vmodamio/typewrt_mark2/images/PXL_20260221_143158114.jpg

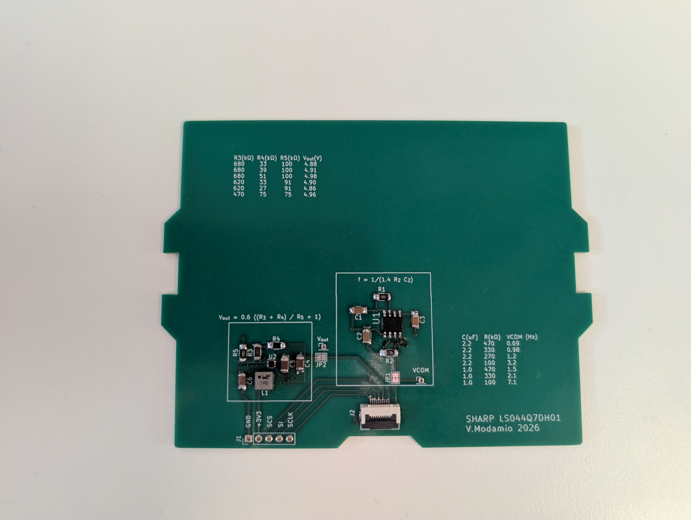
images/PXL_20260221_143158114.jpg
