vmodamio/typewrt_mark2/images/PXL_20260221_143226944.jpg

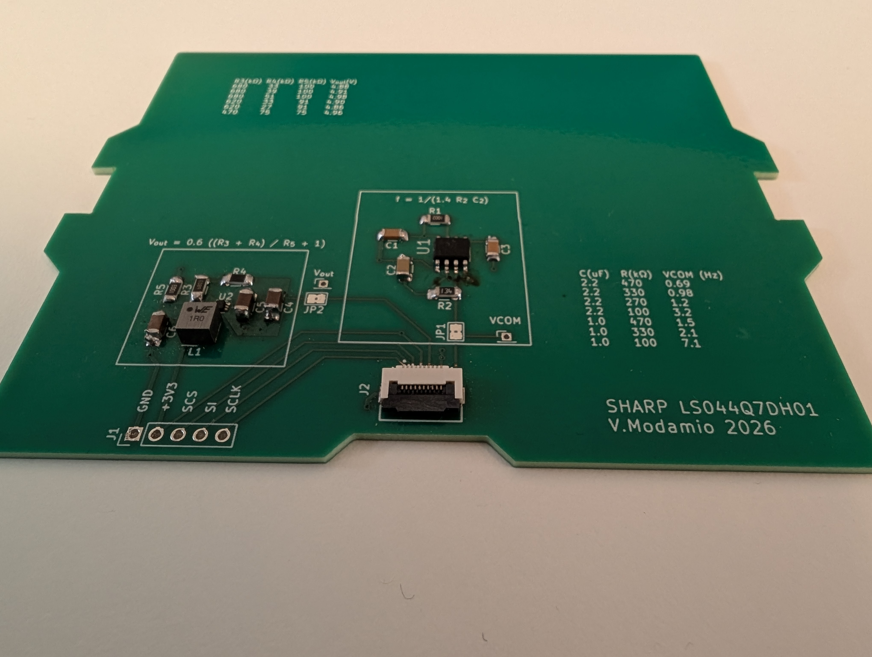
images/PXL_20260221_143226944.jpg
