vmodamio/typewrt_mark2/images/PXL_20260221_143322135.jpg

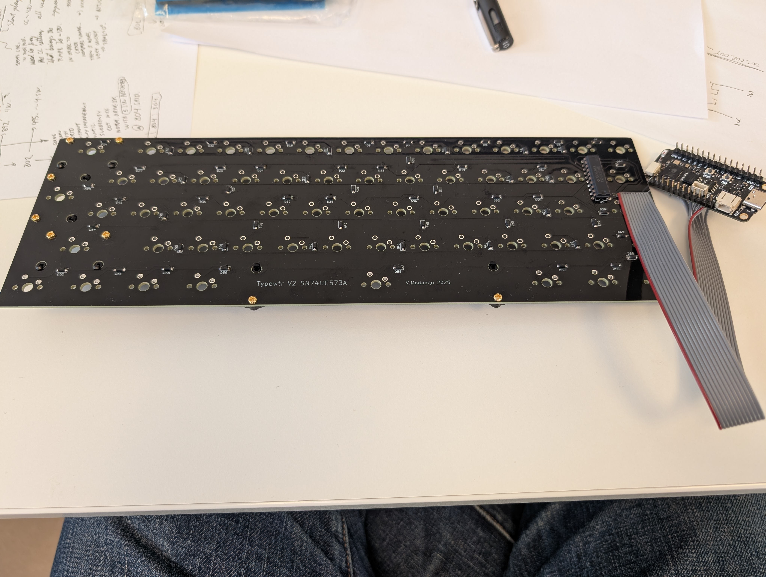
images/PXL_20260221_143322135.jpg
