vmodamio/typewrt_mark2/images/PXL_20260221_143605408.jpg

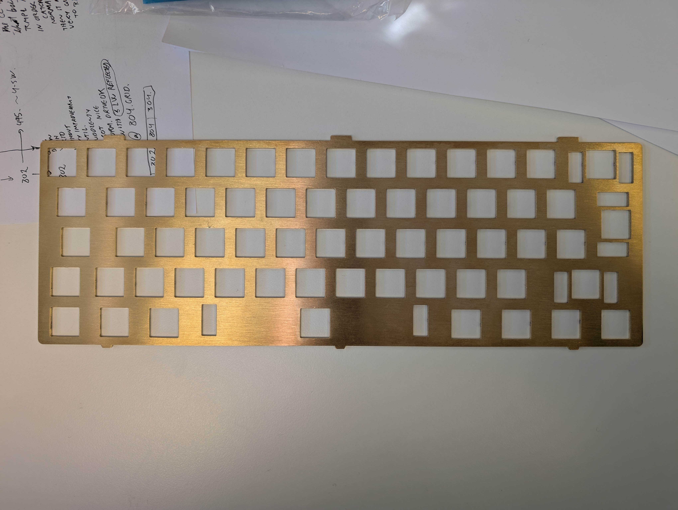
images/PXL_20260221_143605408.jpg
