vmodamio/typewrt_mark2/images/PXL_20260221_144143842.jpg

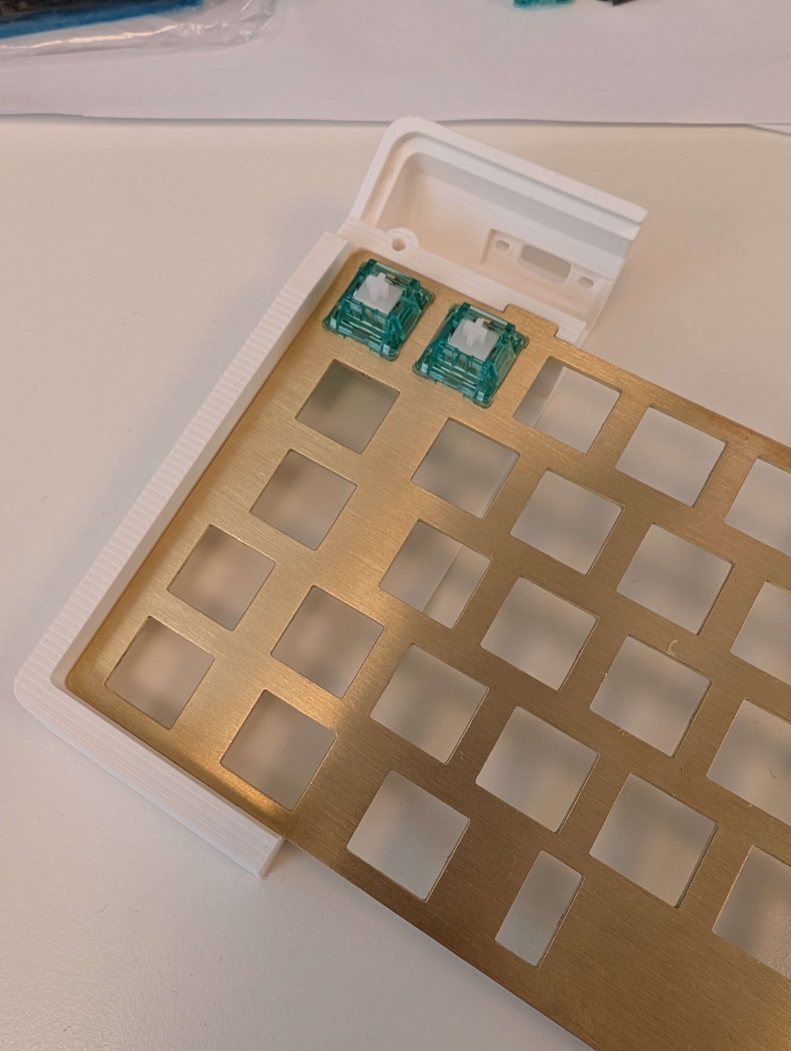
images/PXL_20260221_144143842.jpg
