vmodamio/typewrt_mark2/images/PXL_20260221_162343573.jpg

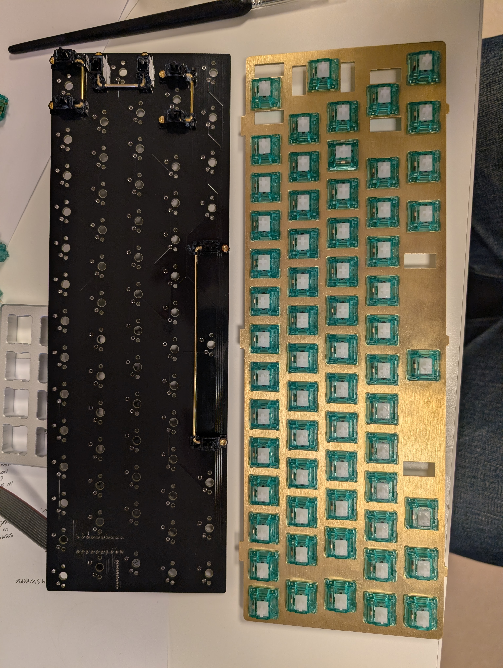
images/PXL_20260221_162343573.jpg
