vmodamio/typewrt_mark2/images/PXL_20260221_164626102.jpg

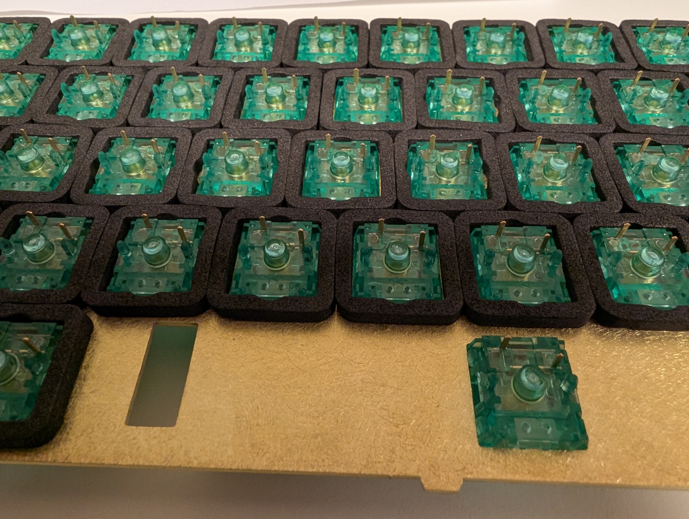
images/PXL_20260221_164626102.jpg
