vmodamio/typewrt_mark2/images/PXL_20260221_170008910.jpg

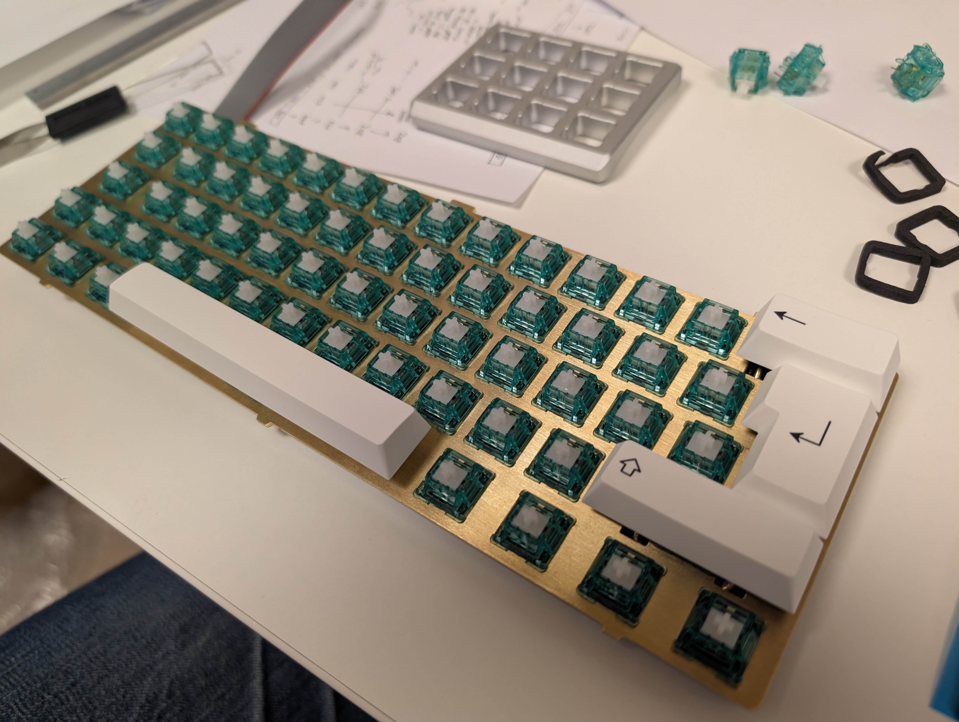
images/PXL_20260221_170008910.jpg
