vmodamio/typewrt_mark2/images/PXL_20260225_174053376.jpg

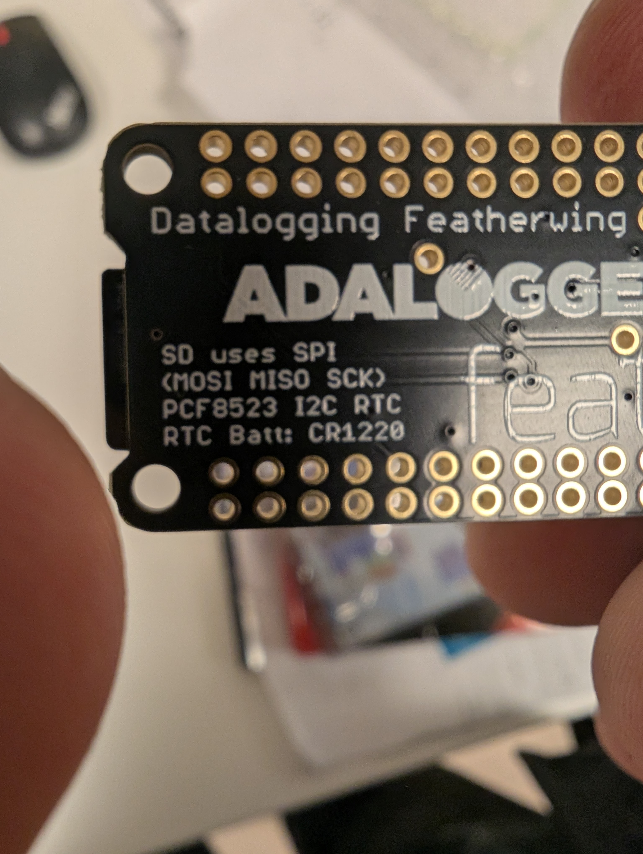
images/PXL_20260225_174053376.jpg
