vmodamio/typewrt_mark2/images/PXL_20260226_163334351.jpg

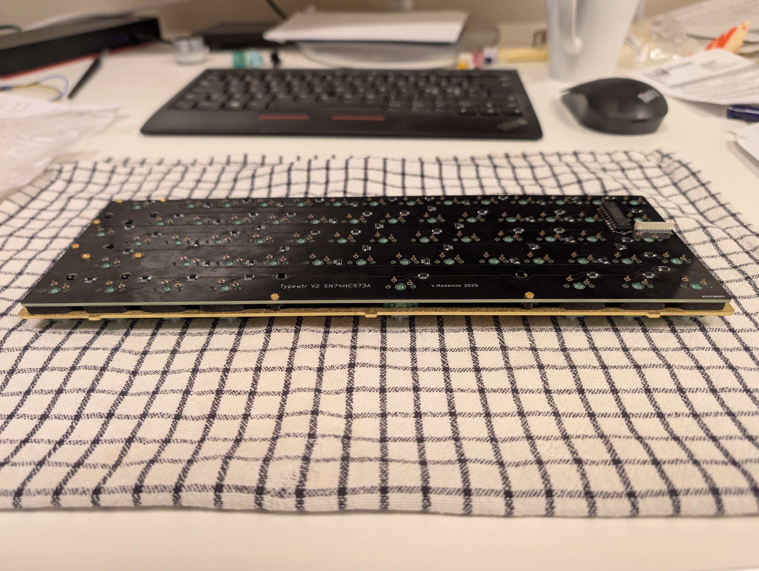
images/PXL_20260226_163334351.jpg
