vmodamio/typewrt_mark2/images/PXL_20260226_163400330.jpg

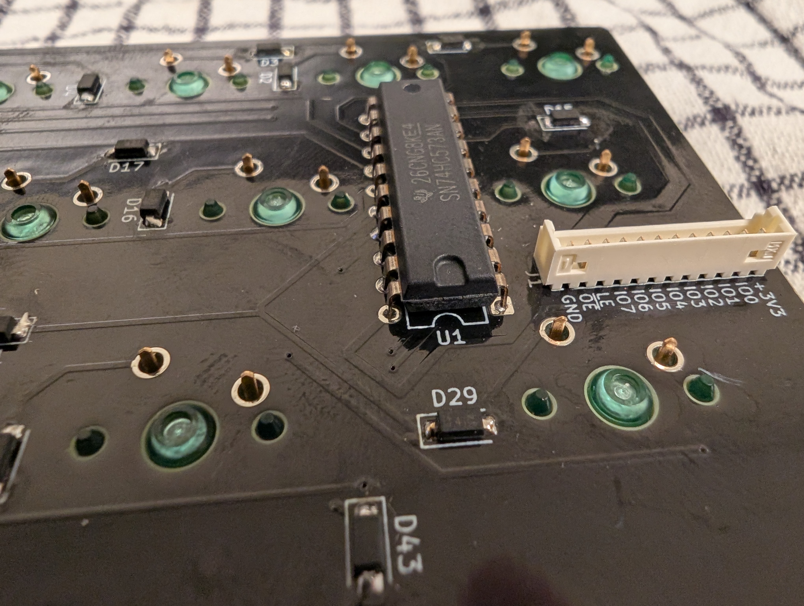
images/PXL_20260226_163400330.jpg
