vmodamio/typewrt_mark2/images/PXL_20260226_171633892.jpg

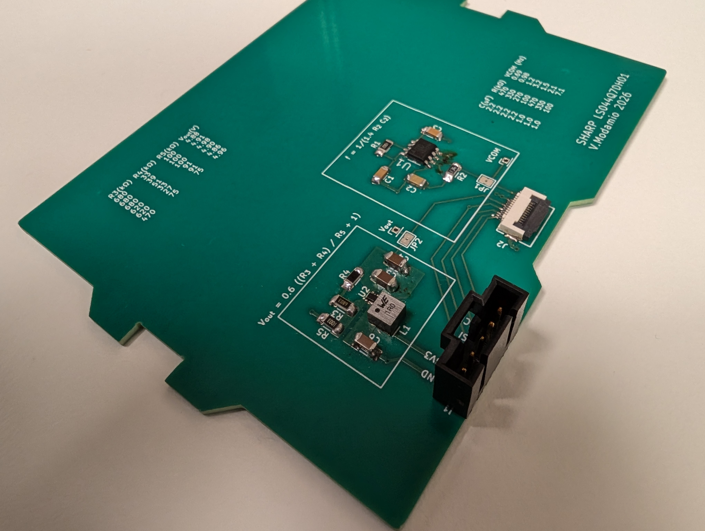
images/PXL_20260226_171633892.jpg
