vmodamio/typewrt_mark2/images/PXL_20260226_174025319.jpg

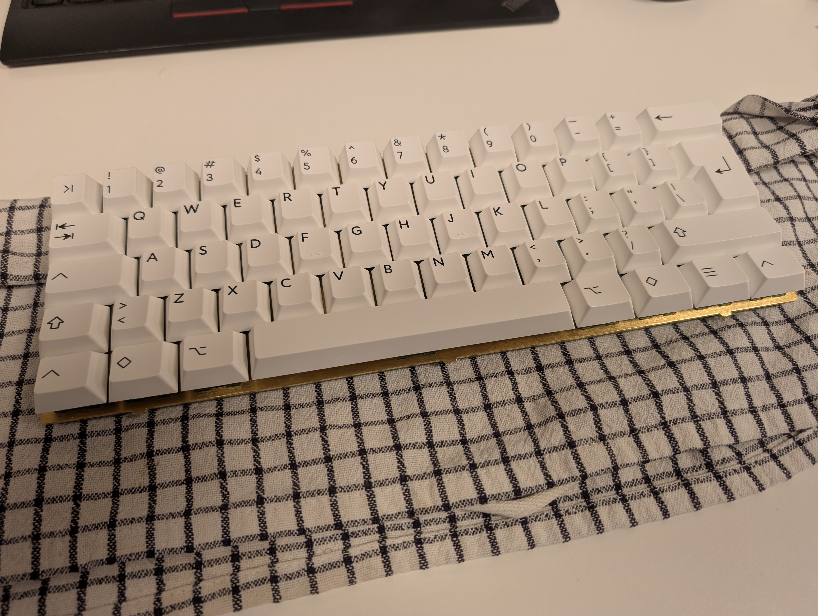
images/PXL_20260226_174025319.jpg
