vmodamio/typewrt_mark2/images/PXL_20260226_174041446.jpg

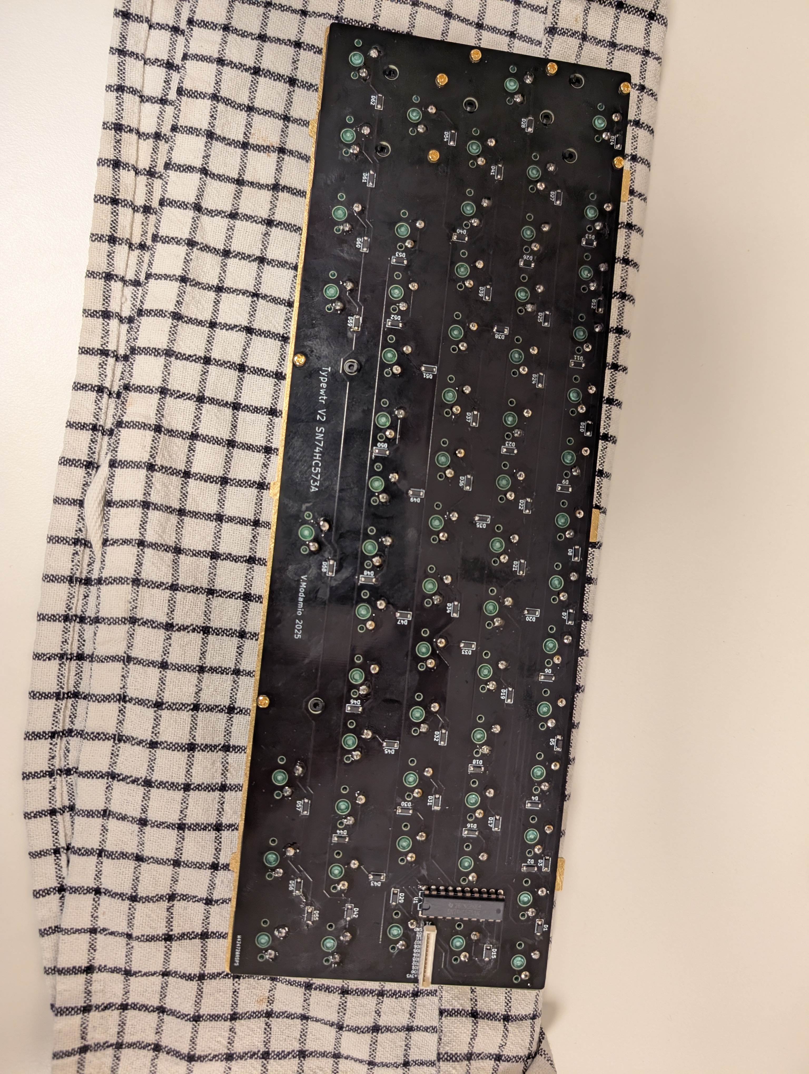
images/PXL_20260226_174041446.jpg
