vmodamio/typewrt_mark2/images/PXL_20260314_165601002.jpg

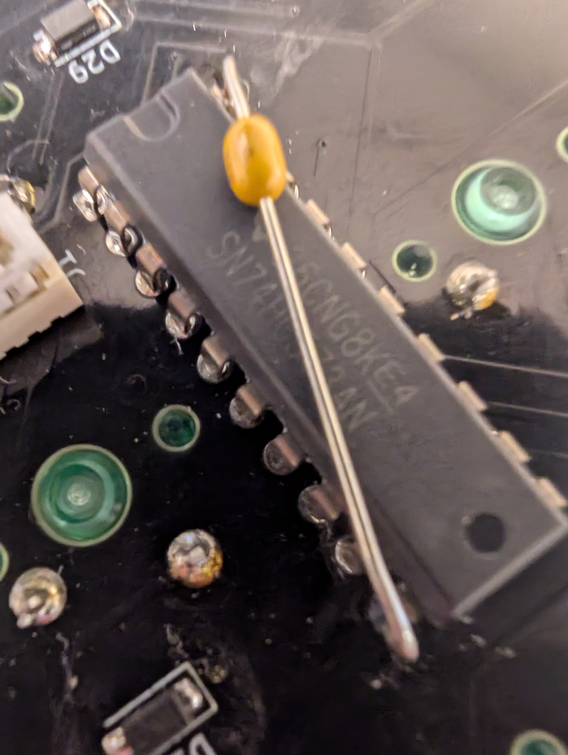
images/PXL_20260314_165601002.jpg
