vmodamio/typewrt_mark2/images/PXL_20260410_063325487.jpg

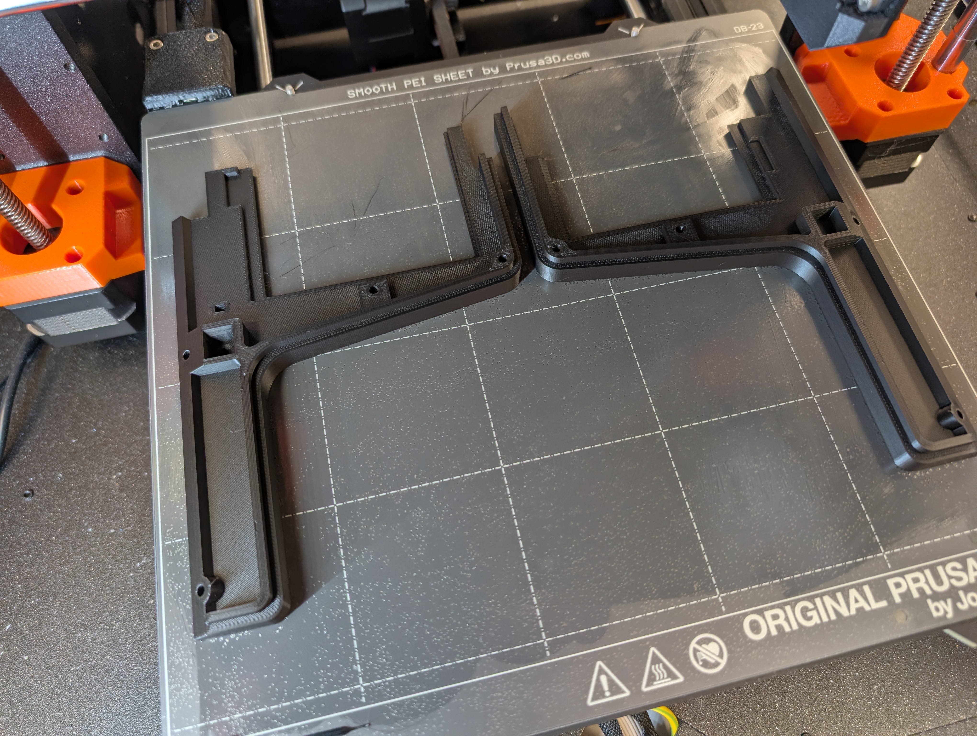
images/PXL_20260410_063325487.jpg
