vmodamio/typewrt_mark2/images/PXL_20260415_064320907.jpg

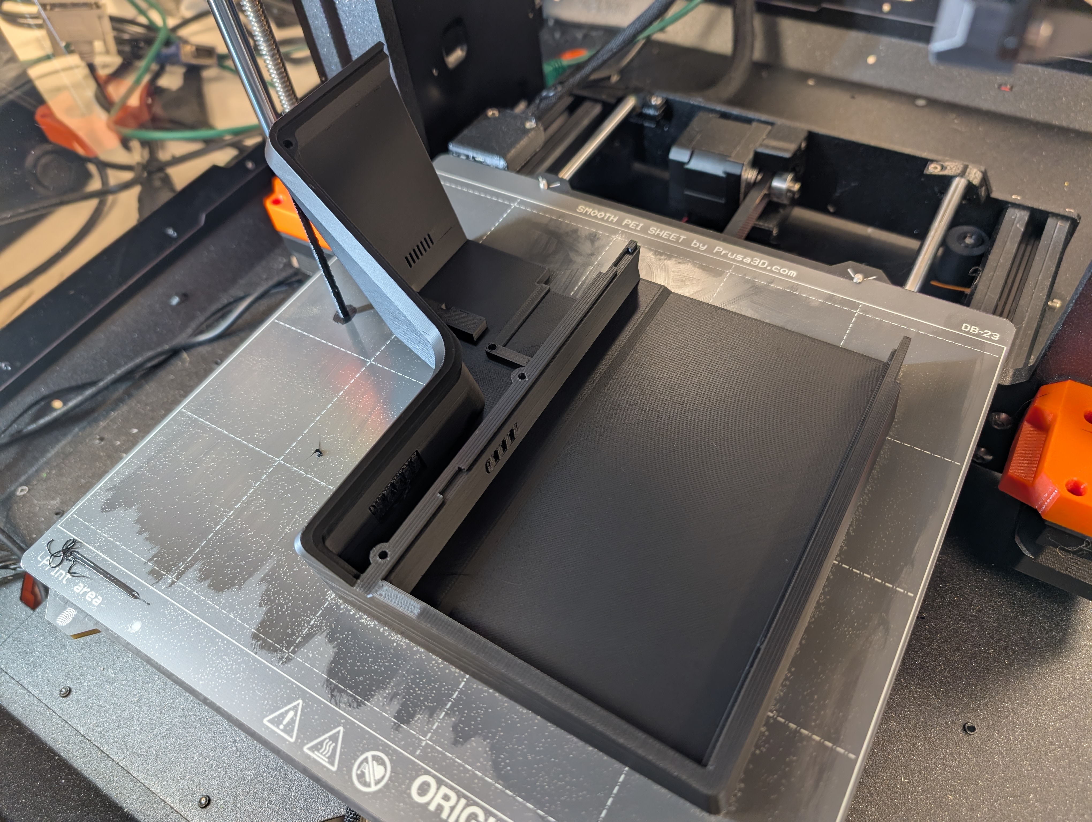
images/PXL_20260415_064320907.jpg
