vmodamio/typewrt_mark2/images/PXL_20260415_064329806.jpg

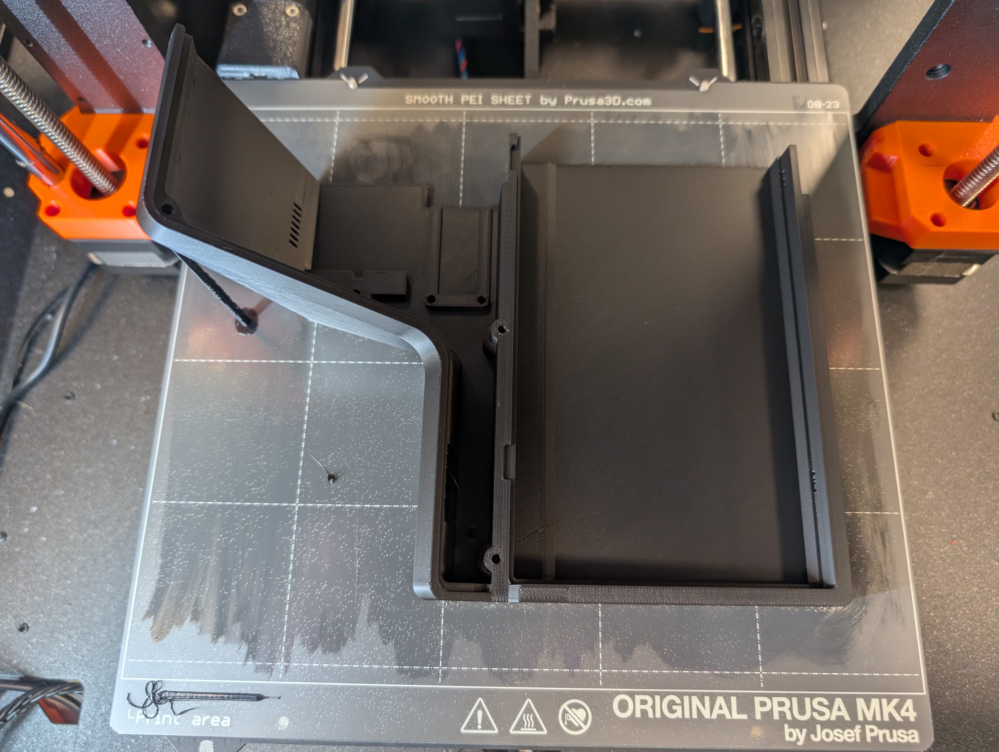
images/PXL_20260415_064329806.jpg
