vmodamio/typewrt_mark2/images/PXL_20260417_130614644.jpg

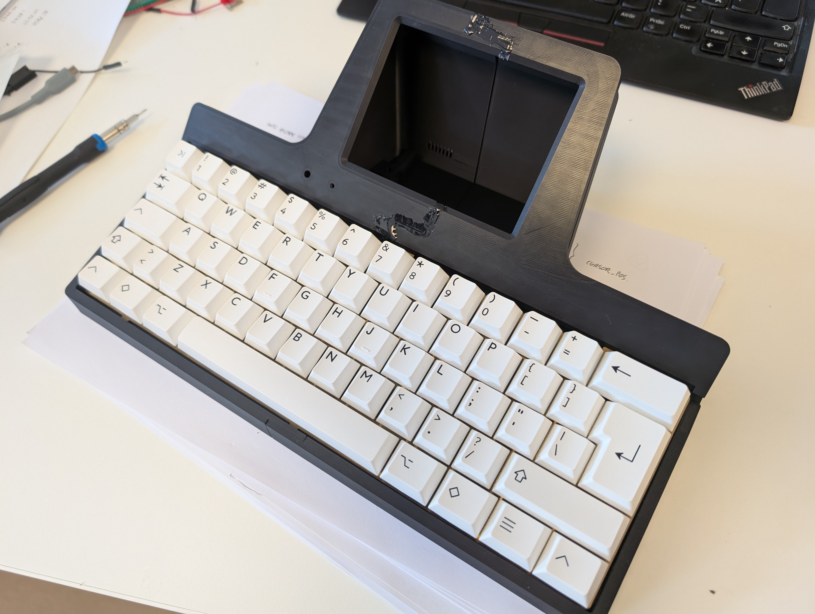
images/PXL_20260417_130614644.jpg
