vmodamio/typewrt_mark2/images/PXL_20260417_132344791.jpg

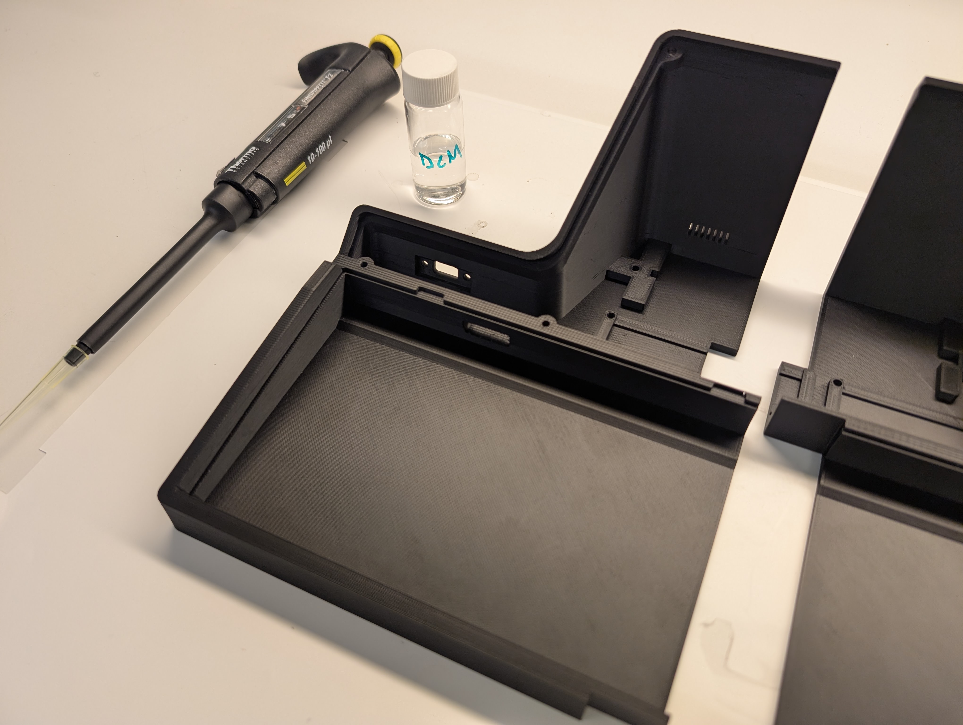
images/PXL_20260417_132344791.jpg
