vmodamio/typewrt_mark2/images/PXL_20260418_184916535.jpg

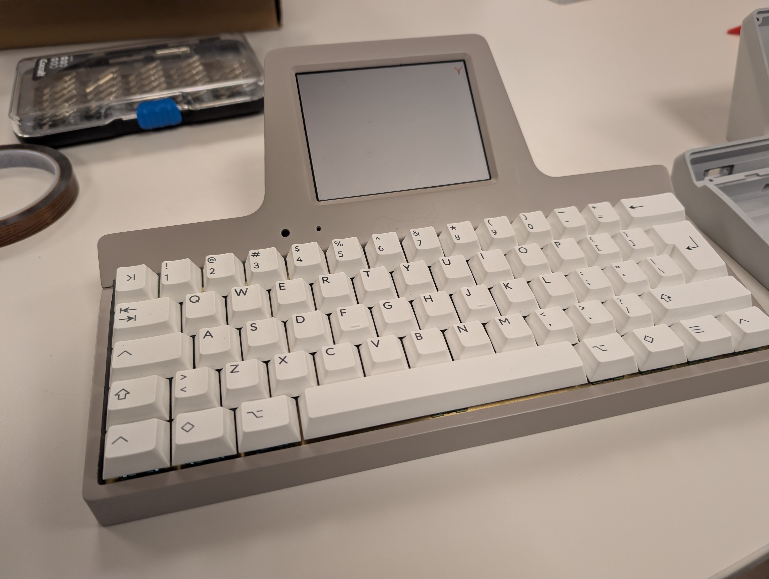
images/PXL_20260418_184916535.jpg
