vmodamio/typewrt_mark2/images/PXL_20260419_162418170.jpg

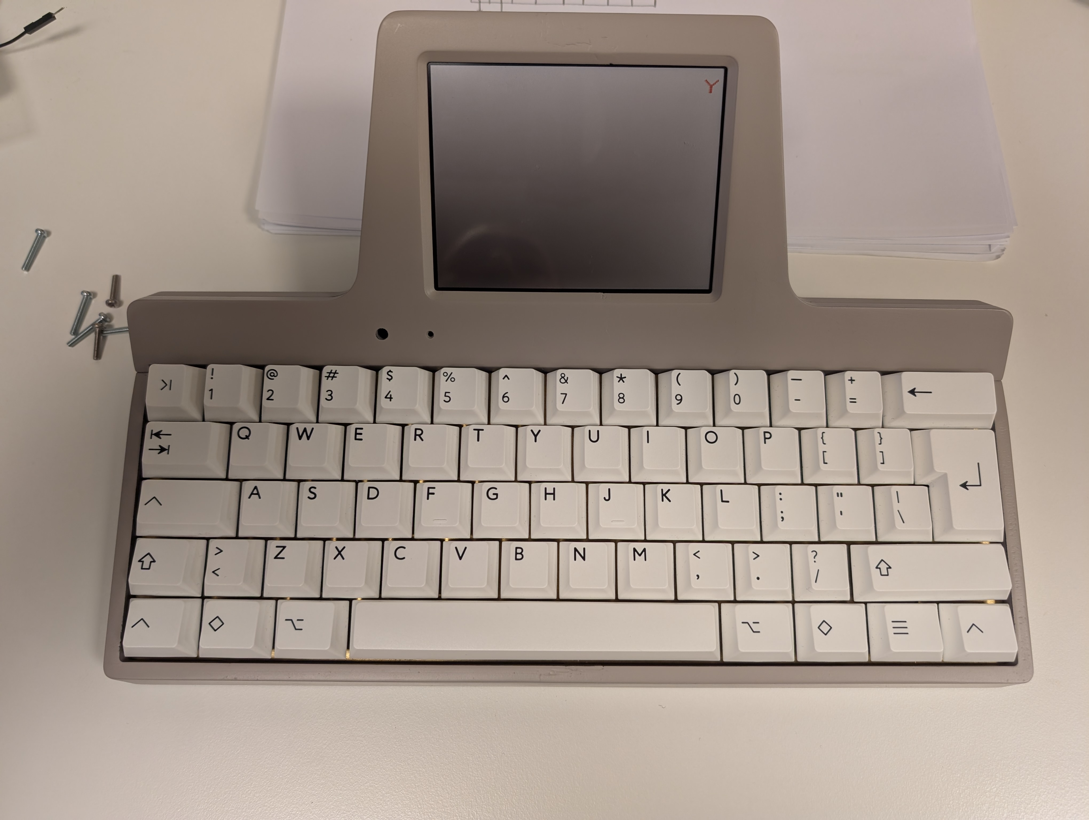
images/PXL_20260419_162418170.jpg
