vmodamio/typewrt_mark2/images/PXL_20260506_173434190.jpg

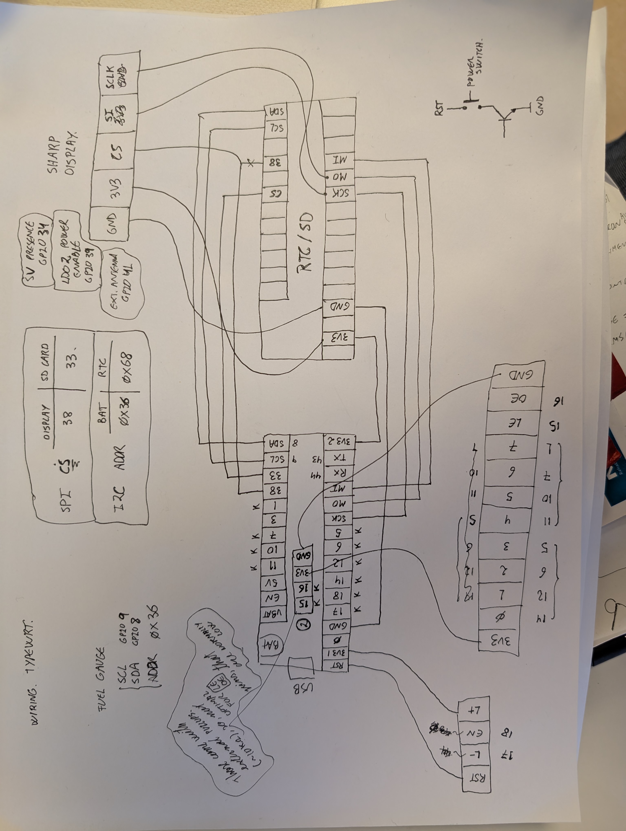
images/PXL_20260506_173434190.jpg
