vmodamio/typewrt_mark2/images/PXL_20260507_135444508.jpg

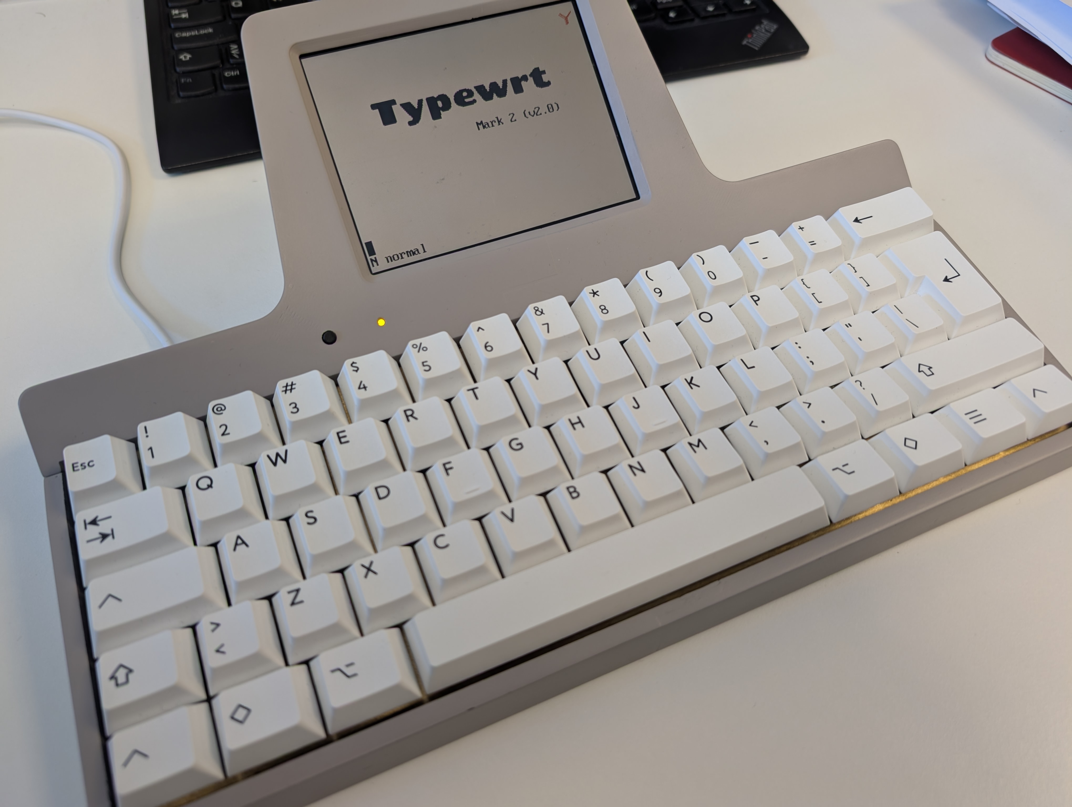
images/PXL_20260507_135444508.jpg
