vmodamio/typewrt_mark2/images/PXL_20260515_155124877.jpg

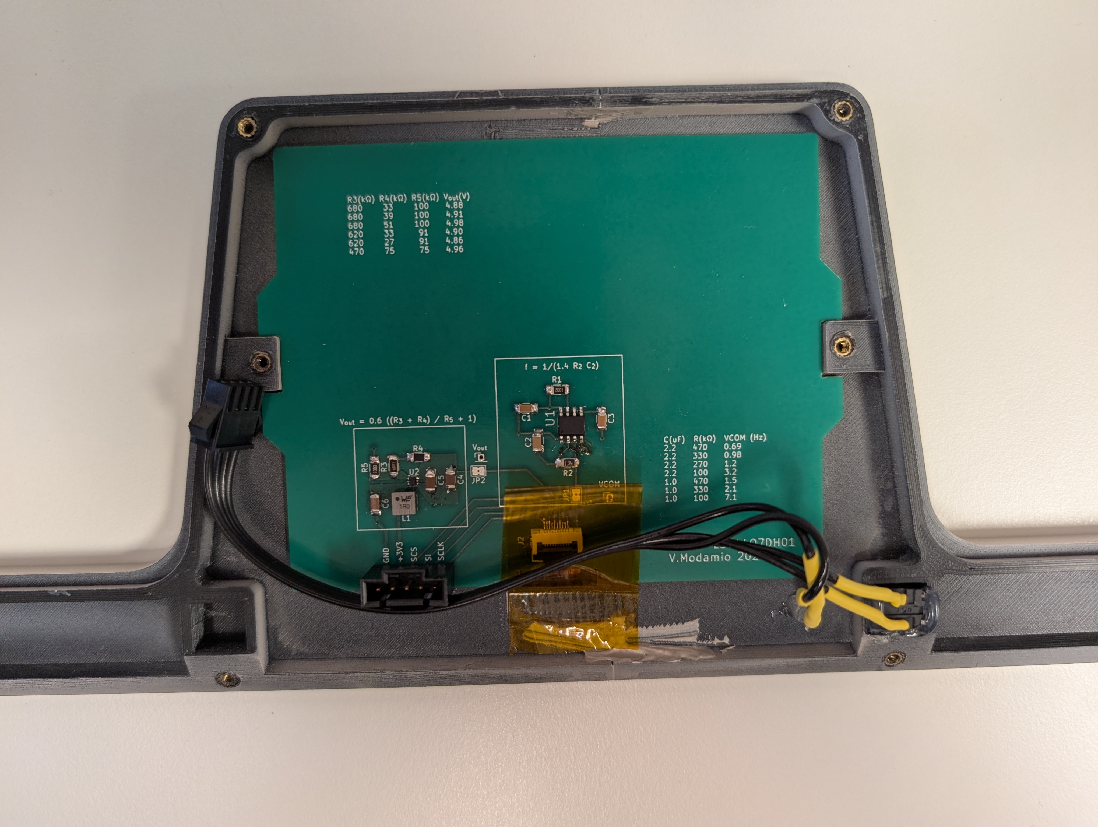
images/PXL_20260515_155124877.jpg
