vmodamio/typewrt_mark2/images/PXL_20260515_155157424.jpg

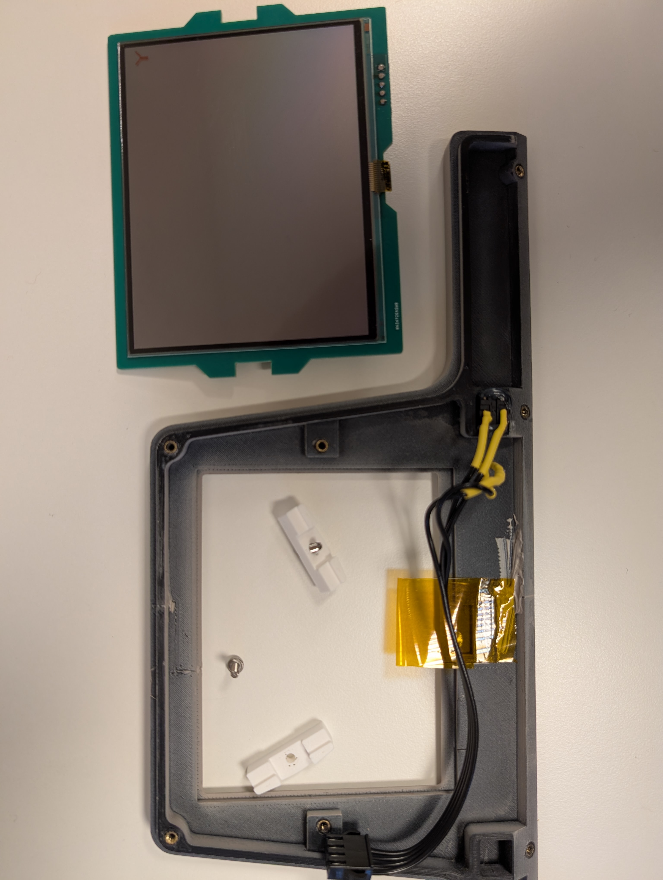
images/PXL_20260515_155157424.jpg
