vmodamio/typewrt_mark2/images/PXL_20260515_160353344.jpg

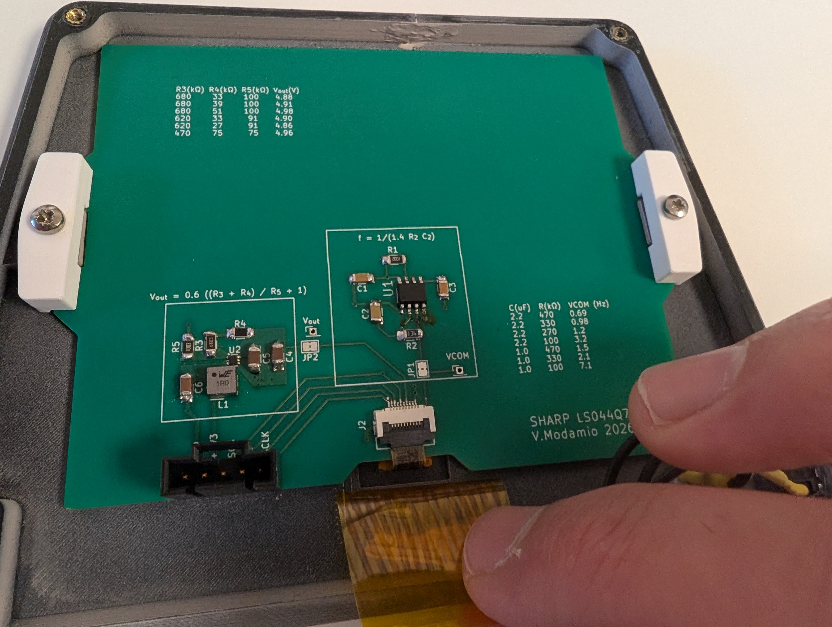
images/PXL_20260515_160353344.jpg
