vmodamio/typewrt_mark2/images/PXL_20260515_160508526.jpg

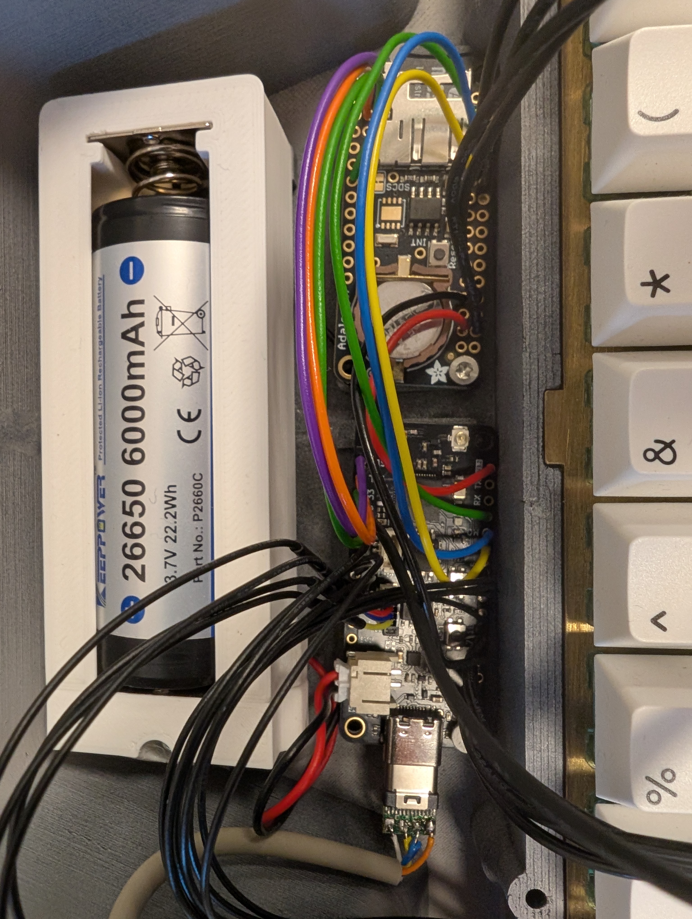
images/PXL_20260515_160508526.jpg
