vmodamio/typewrt_mark2/images/PXL_20260515_160546878.jpg

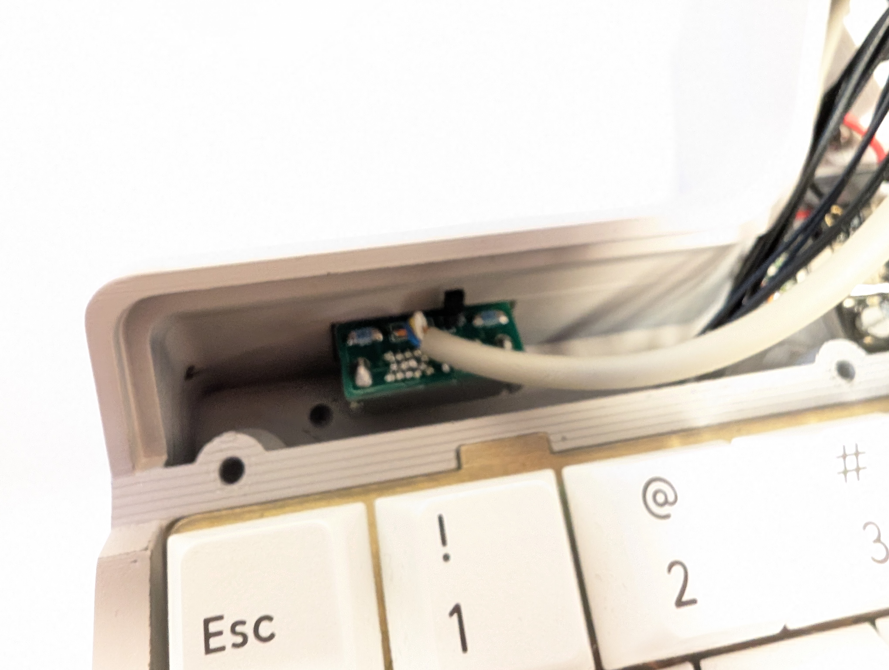
images/PXL_20260515_160546878.jpg
