vmodamio/typewrt_mark2/images/PXL_20260515_161025579.jpg

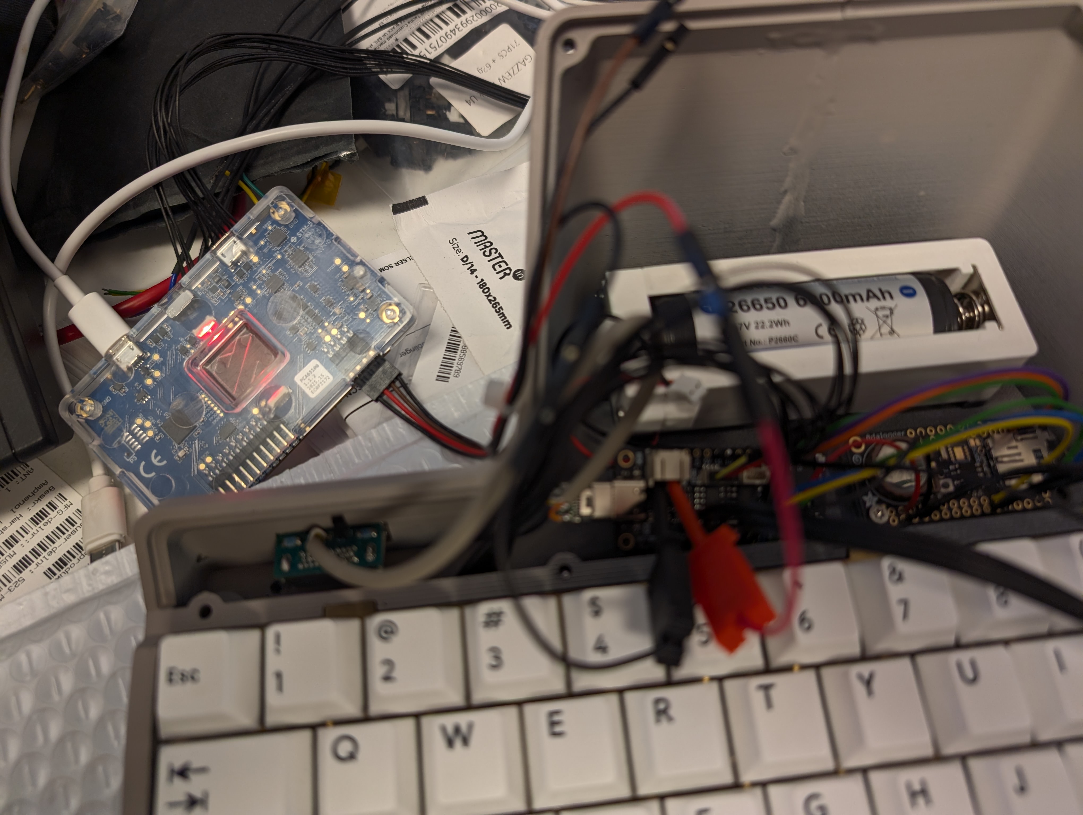
images/PXL_20260515_161025579.jpg
