vmodamio/typewrt_mark2/images/PXL_20260518_174359410.jpg

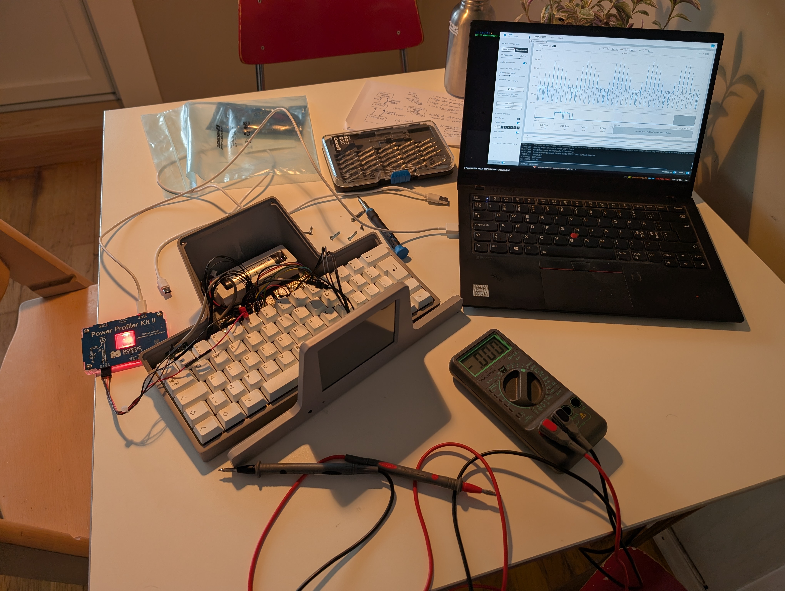
images/PXL_20260518_174359410.jpg
