vmodamio/typewrt_mark2/images/PXL_20260601_181731286.jpg

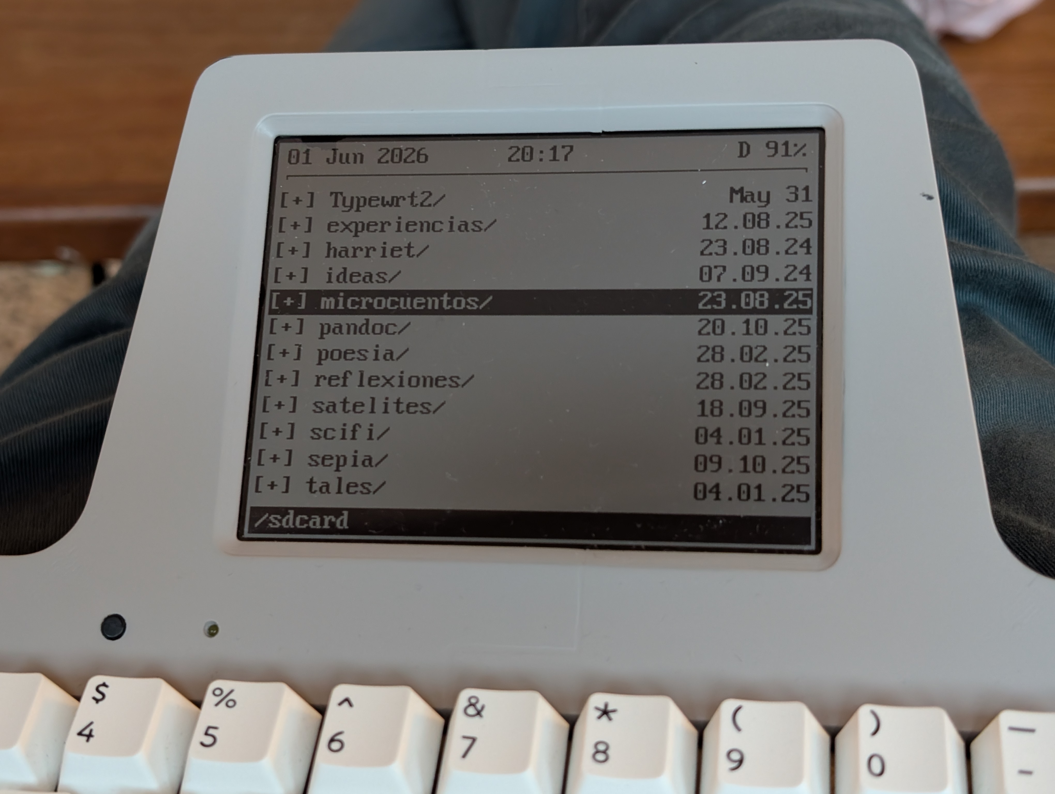
images/PXL_20260601_181731286.jpg
