vmodamio/typewrt_mark2/images/PXL_20260603_174718972.jpg

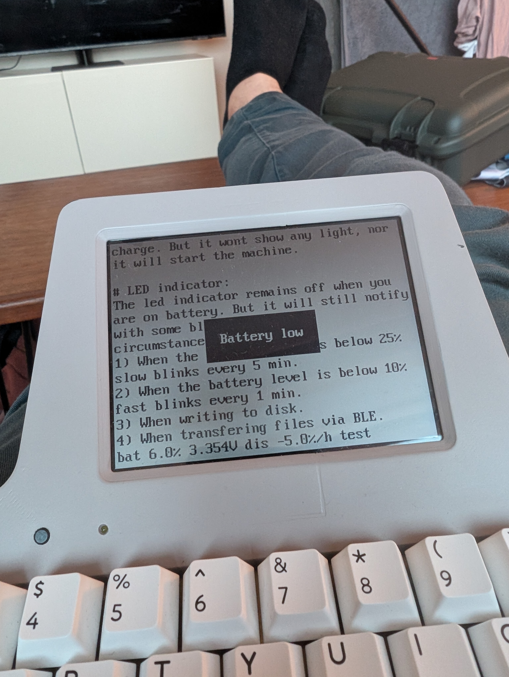
images/PXL_20260603_174718972.jpg
